sugerslp/zmk-config/kicad_data_Title72/Title72.kicad_sch

## KiCad design kicad_data_Title72/Title72.kicad_sch (2025-01-29)

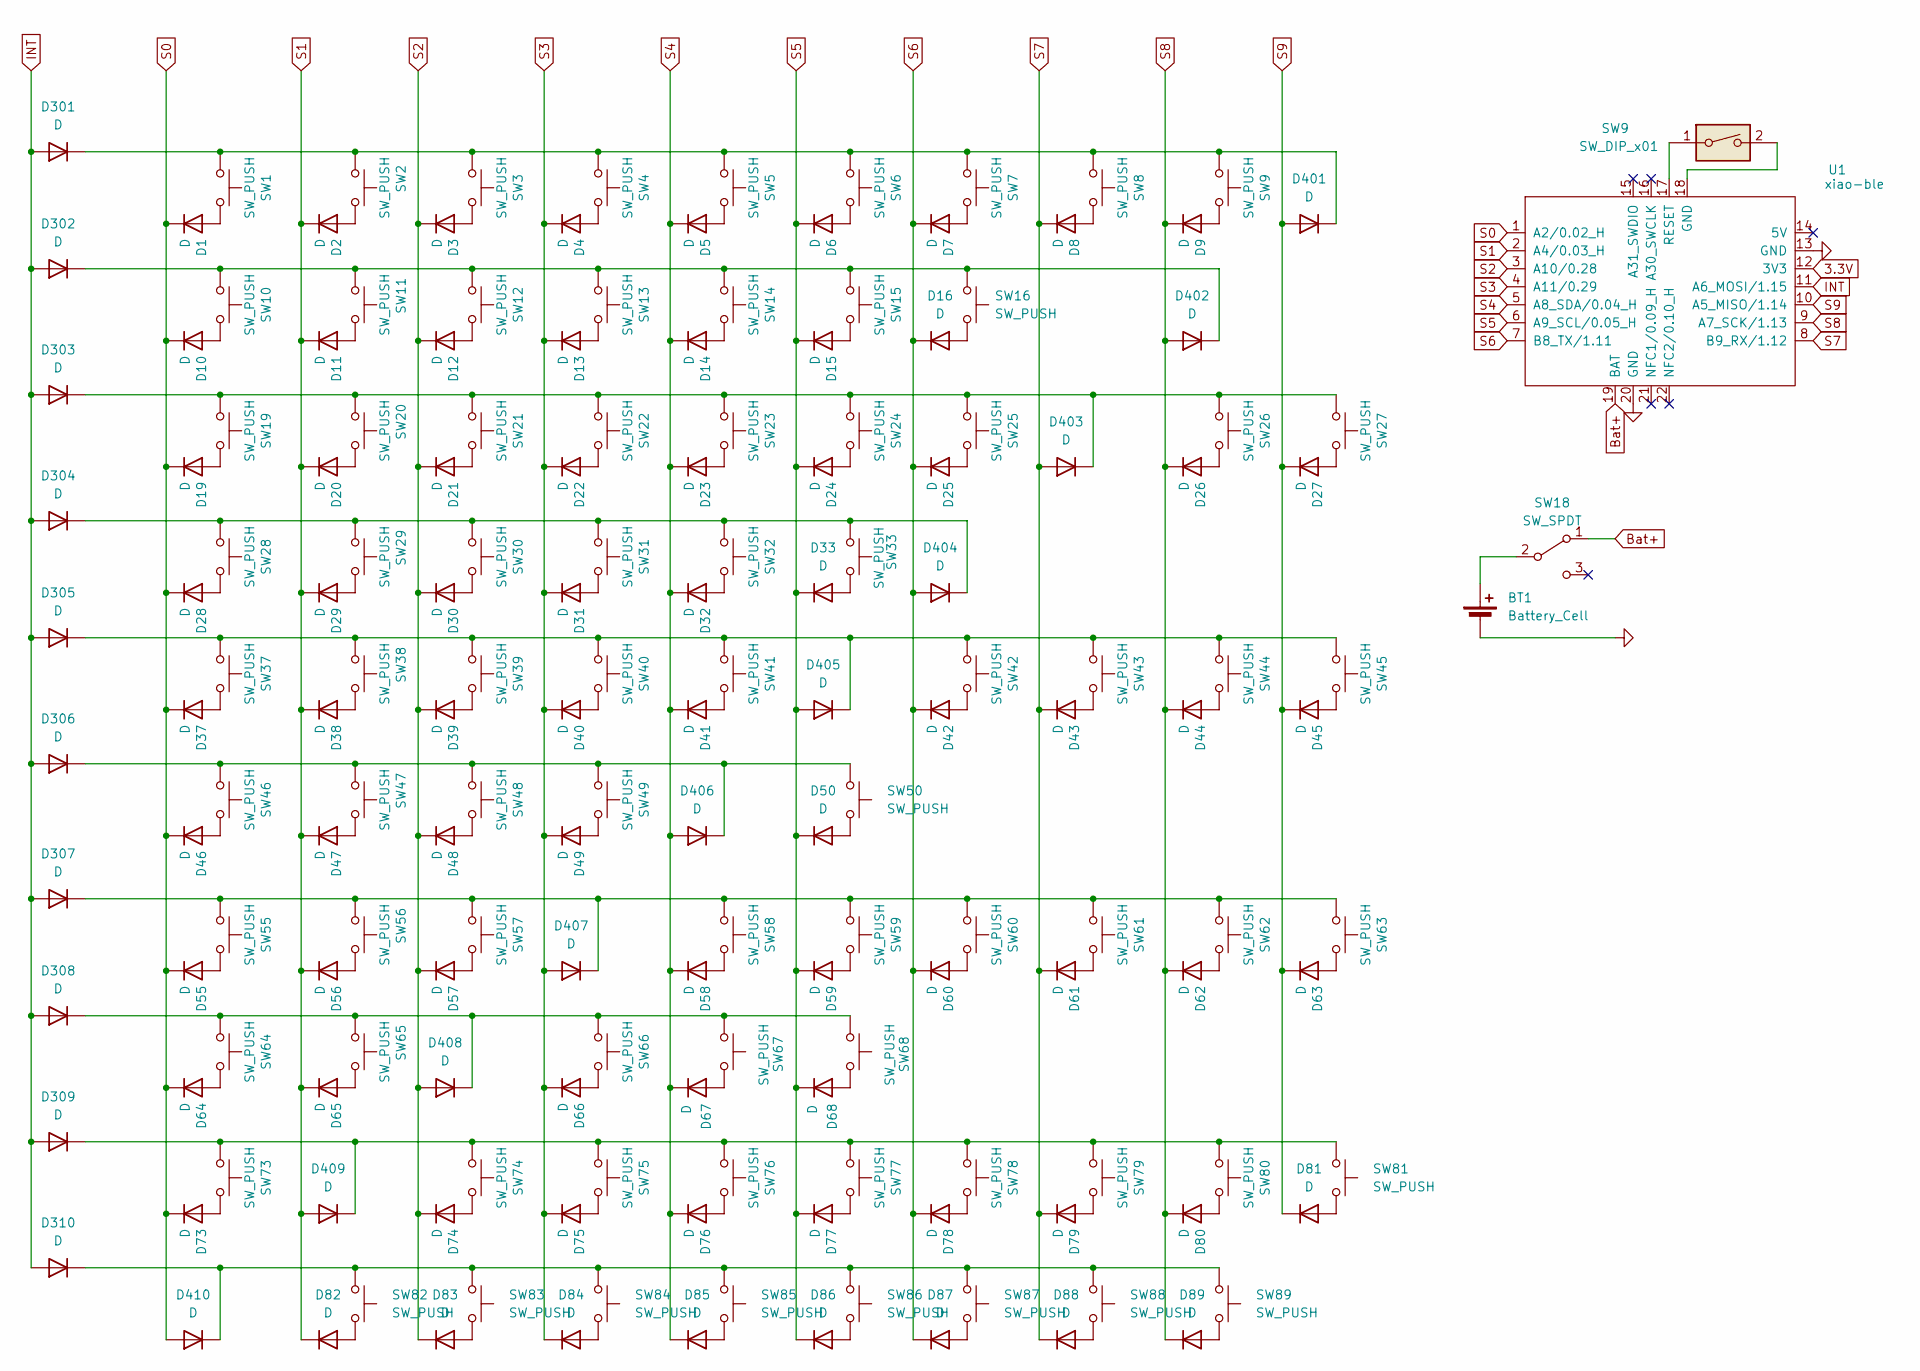
[picture p2: schematic Title72.kicad_sch]

Parts:
BT1: Battery_Cell; Battery_ali_CR1632
D1, D2, D3, D4, D5, D6, D7, D8, D9, D10, D11, D12, D13, D14, D15, D16, D19, D20, D21, D22, D23, D24, D25, D26, D27, D28, D29, D30, D31, D32, D33, D37, D38, D39, D40, D41, D42, D43, D44, D45, D46, D47, D48, D49, D50, D55, D56, D57, D58, D59, D60, D61, D62, D63, D64, D65, D66, D67, D68, D73, D74, D75, D76, D77, D78, D79, D80, D81, D82, D83, D84, D85, D86, D87, D88, D89, D301, D302, D303, D304, D305, D306, D307, D308, D309, D310, D401, D402, D403, D404, D405, D406, D407, D408, D409, D410: D; D_SOD-123
SW1, SW2, SW3, SW4, SW5, SW6, SW7, SW8, SW10, SW11, SW12, SW13, SW14, SW15, SW16, SW19, SW20, SW21, SW22, SW23, SW24, SW25, SW26, SW27, SW28, SW29, SW30, SW31, SW32, SW33, SW37, SW38, SW39, SW40, SW41, SW42, SW43, SW44, SW45, SW46, SW47, SW48, SW49, SW50, SW55, SW56, SW57, SW58, SW59, SW60, SW61, SW62, SW63, SW64, SW65, SW66, SW67, SW68, SW73, SW74, SW75, SW76, SW77, SW78, SW79, SW80, SW81, SW82, SW83, SW84, SW85, SW86, SW87, SW88, SW89: SW_PUSH; Choc_v2_Hotswap_1u
SW9: SW_DIP_x01; ResetSW
SW18: SW_SPDT; SW_SPDT_PCM12
U1: xiao-ble; xiao-ble-tht

Connections:
3.3V: U1.12 (3V3)
Bat+: SW18.1 (A), U1.19 (BAT)
GND: BT1.2 (-), U1.13 (GND), U1.20 (GND)
INT: D301.2 (A), D302.2 (A), D303.2 (A), D304.2 (A), D305.2 (A), D306.2 (A), D307.2 (A), D308.2 (A), D309.2 (A), D310.2 (A), U1.11 (A6_MOSI/1.15)
unnamed: BT1.1 (+), SW18.2 (B)
unnamed: D1.2 (A), SW1.2
unnamed: D2.2 (A), SW2.2
unnamed: D3.2 (A), SW3.2
unnamed: D4.2 (A), SW4.2
unnamed: D5.2 (A), SW5.2
unnamed: D6.2 (A), SW6.2
unnamed: D7.2 (A), SW7.2
unnamed: D8.2 (A), SW8.2
unnamed: D9.2 (A), SW9.2
unnamed: D10.2 (A), SW10.2
unnamed: D11.2 (A), SW11.2
unnamed: D12.2 (A), SW12.2
unnamed: D13.2 (A), SW13.2
unnamed: D14.2 (A), SW14.2
unnamed: D15.2 (A), SW15.2
unnamed: D16.2 (A), SW16.2
unnamed: D19.2 (A), SW19.2
unnamed: D20.2 (A), SW20.2
unnamed: D21.2 (A), SW21.2
unnamed: D22.2 (A), SW22.2
unnamed: D23.2 (A), SW23.2
unnamed: D24.2 (A), SW24.2
unnamed: D25.2 (A), SW25.2
unnamed: D26.2 (A), SW26.2
unnamed: D27.2 (A), SW27.2
unnamed: D28.2 (A), SW28.2
unnamed: D29.2 (A), SW29.2
unnamed: D30.2 (A), SW30.2
unnamed: D31.2 (A), SW31.2
unnamed: D32.2 (A), SW32.2
unnamed: D33.2 (A), SW33.2
unnamed: D37.2 (A), SW37.2
unnamed: D38.2 (A), SW38.2
unnamed: D39.2 (A), SW39.2
unnamed: D40.2 (A), SW40.2
unnamed: D41.2 (A), SW41.2
unnamed: D42.2 (A), SW42.2
unnamed: D43.2 (A), SW43.2
unnamed: D44.2 (A), SW44.2
unnamed: D45.2 (A), SW45.2
unnamed: D46.2 (A), SW46.2
unnamed: D47.2 (A), SW47.2
unnamed: D48.2 (A), SW48.2
unnamed: D49.2 (A), SW49.2
unnamed: D50.2 (A), SW50.2
unnamed: D55.2 (A), SW55.2
unnamed: D56.2 (A), SW56.2
unnamed: D57.2 (A), SW57.2
unnamed: D58.2 (A), SW58.2
unnamed: D59.2 (A), SW59.2
unnamed: D60.2 (A), SW60.2
unnamed: D61.2 (A), SW61.2
unnamed: D62.2 (A), SW62.2
unnamed: D63.2 (A), SW63.2
unnamed: D64.2 (A), SW64.2
unnamed: D65.2 (A), SW65.2
unnamed: D66.2 (A), SW66.2
unnamed: D67.2 (A), SW67.2
unnamed: D68.2 (A), SW68.2
unnamed: D73.2 (A), SW73.2
unnamed: D74.2 (A), SW74.2
unnamed: D75.2 (A), SW75.2
unnamed: D76.2 (A), SW76.2
unnamed: D77.2 (A), SW77.2
unnamed: D78.2 (A), SW78.2
unnamed: D79.2 (A), SW79.2
unnamed: D80.2 (A), SW80.2
unnamed: D81.2 (A), SW81.2
unnamed: D82.2 (A), SW82.2
unnamed: D83.2 (A), SW83.2
unnamed: D84.2 (A), SW84.2
unnamed: D85.2 (A), SW85.2
unnamed: D86.2 (A), SW86.2
unnamed: D87.2 (A), SW87.2
unnamed: D88.2 (A), SW88.2
unnamed: D89.2 (A), SW89.2
unnamed: D301.1 (K), D401.1 (K), SW1.1, SW2.1, SW3.1, SW4.1, SW5.1, SW6.1, SW7.1, SW8.1, SW9.1
unnamed: D302.1 (K), D402.1 (K), SW10.1, SW11.1, SW12.1, SW13.1, SW14.1, SW15.1, SW16.1
unnamed: D303.1 (K), D403.1 (K), SW19.1, SW20.1, SW21.1, SW22.1, SW23.1, SW24.1, SW25.1, SW26.1, SW27.1
unnamed: D304.1 (K), D404.1 (K), SW28.1, SW29.1, SW30.1, SW31.1, SW32.1, SW33.1
unnamed: D305.1 (K), D405.1 (K), SW37.1, SW38.1, SW39.1, SW40.1, SW41.1, SW42.1, SW43.1, SW44.1, SW45.1
unnamed: D306.1 (K), D406.1 (K), SW46.1, SW47.1, SW48.1, SW49.1, SW50.1
unnamed: D307.1 (K), D407.1 (K), SW55.1, SW56.1, SW57.1, SW58.1, SW59.1, SW60.1, SW61.1, SW62.1, SW63.1
unnamed: D308.1 (K), D408.1 (K), SW64.1, SW65.1, SW66.1, SW67.1, SW68.1
unnamed: D309.1 (K), D409.1 (K), SW73.1, SW74.1, SW75.1, SW76.1, SW77.1, SW78.1, SW79.1, SW80.1, SW81.1
unnamed: D310.1 (K), D410.1 (K), SW82.1, SW83.1, SW84.1, SW85.1, SW86.1, SW87.1, SW88.1, SW89.1
unnamed: SW9.1, U1.17 (RESET)
unnamed: SW9.2, U1.18 (GND)
S0: D1.1 (K), D10.1 (K), D19.1 (K), D28.1 (K), D37.1 (K), D46.1 (K), D55.1 (K), D64.1 (K), D73.1 (K), D410.2 (A), U1.1 (A2/0.02_H)
S1: D2.1 (K), D11.1 (K), D20.1 (K), D29.1 (K), D38.1 (K), D47.1 (K), D56.1 (K), D65.1 (K), D82.1 (K), D409.2 (A), U1.2 (A4/0.03_H)
S2: D3.1 (K), D12.1 (K), D21.1 (K), D30.1 (K), D39.1 (K), D48.1 (K), D57.1 (K), D74.1 (K), D83.1 (K), D408.2 (A), U1.3 (A10/0.28)
S3: D4.1 (K), D13.1 (K), D22.1 (K), D31.1 (K), D40.1 (K), D49.1 (K), D66.1 (K), D75.1 (K), D84.1 (K), D407.2 (A), U1.4 (A11/0.29)
S4: D5.1 (K), D14.1 (K), D23.1 (K), D32.1 (K), D41.1 (K), D58.1 (K), D67.1 (K), D76.1 (K), D85.1 (K), D406.2 (A), U1.5 (A8_SDA/0.04_H)
S5: D6.1 (K), D15.1 (K), D24.1 (K), D33.1 (K), D50.1 (K), D59.1 (K), D68.1 (K), D77.1 (K), D86.1 (K), D405.2 (A), U1.6 (A9_SCL/0.05_H)
S6: D7.1 (K), D16.1 (K), D25.1 (K), D42.1 (K), D60.1 (K), D78.1 (K), D87.1 (K), D404.2 (A), U1.7 (B8_TX/1.11)
S7: D8.1 (K), D43.1 (K), D61.1 (K), D79.1 (K), D88.1 (K), D403.2 (A), U1.8 (B9_RX/1.12)
S8: D9.1 (K), D26.1 (K), D44.1 (K), D62.1 (K), D80.1 (K), D89.1 (K), D402.2 (A), U1.9 (A7_SCK/1.13)
S9: D27.1 (K), D45.1 (K), D63.1 (K), D81.1 (K), D401.2 (A), U1.10 (A5_MISO/1.14)
